vdesselwout/blade-scraper/drawings/v7/bottom.png

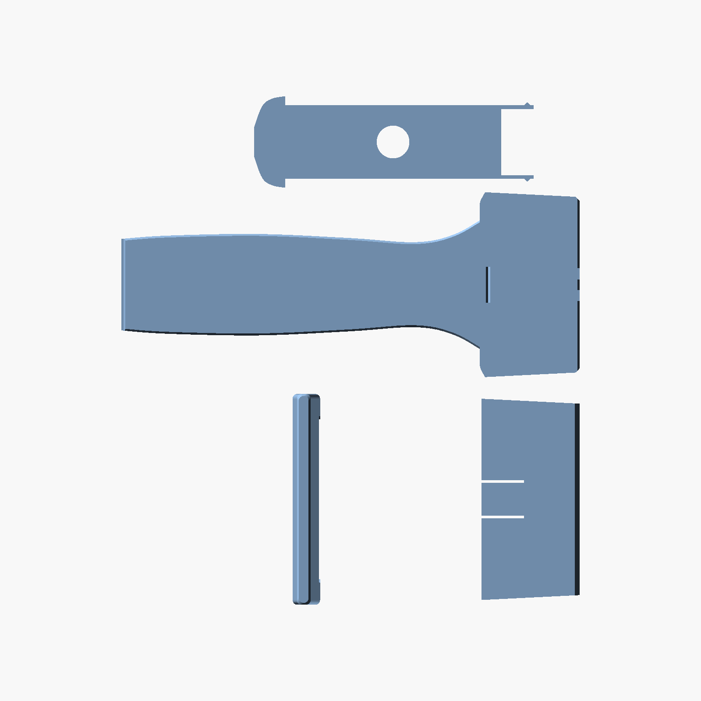
drawings/v7/bottom.png
