vdesselwout/blade-scraper/drawings/v7/drawing.png

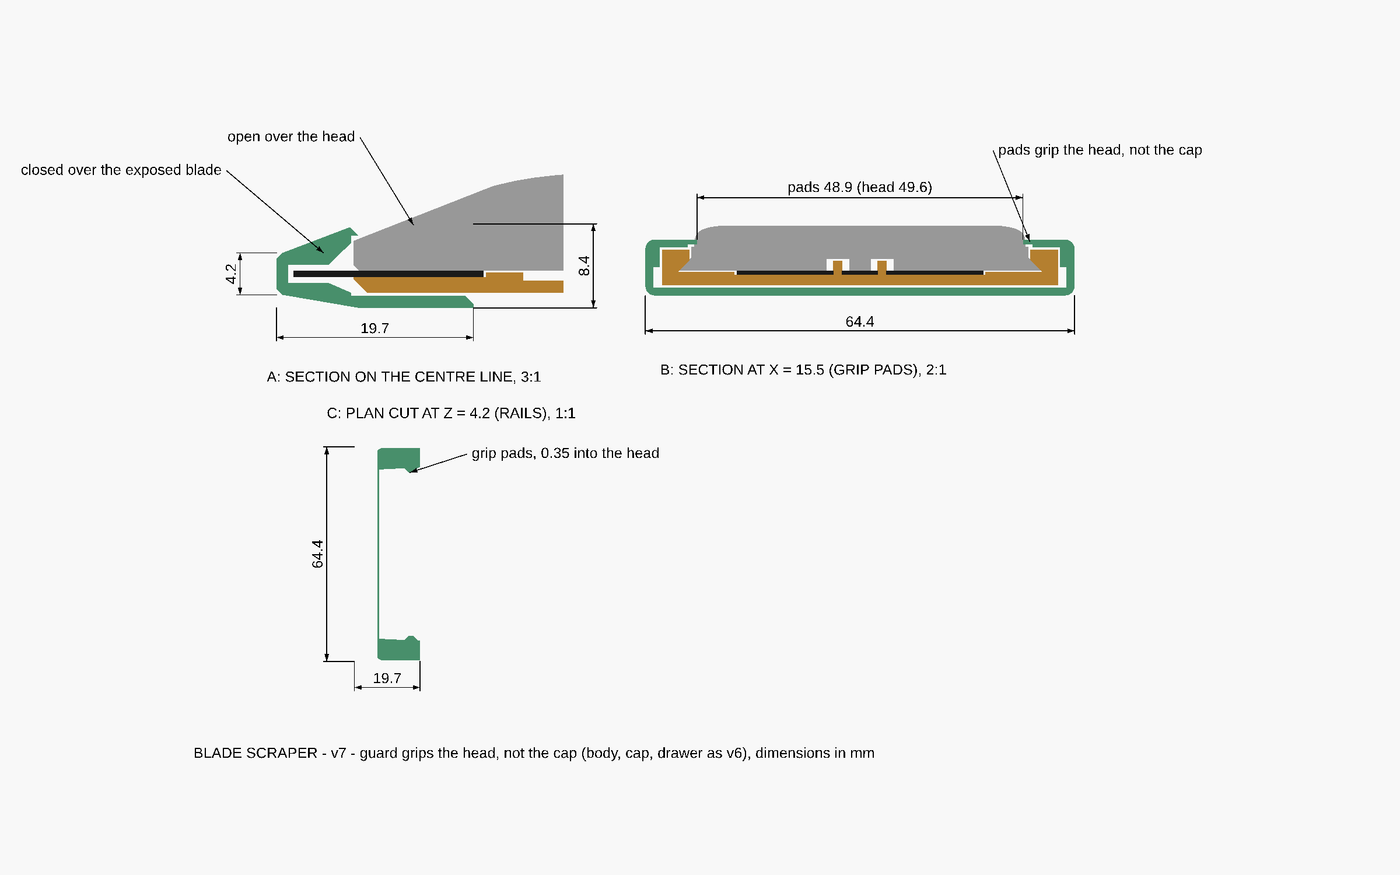
drawings/v7/drawing.png
