vdesselwout/blade-scraper/drawings/v7/guard-bottom.png

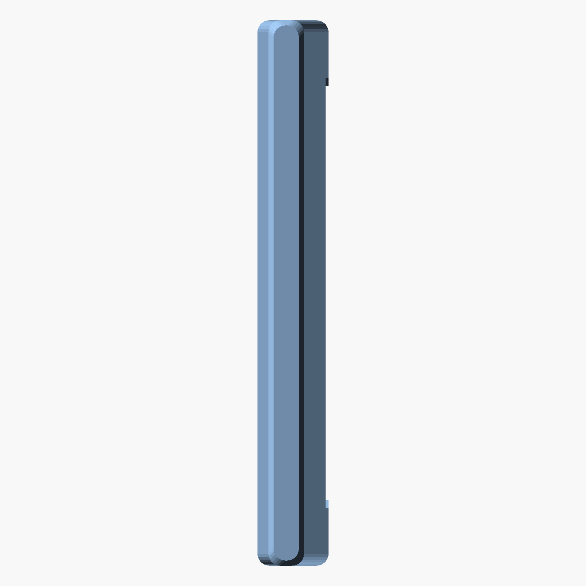
drawings/v7/guard-bottom.png
