vdesselwout/blade-scraper/drawings/v7/guard-iso-bottom.png

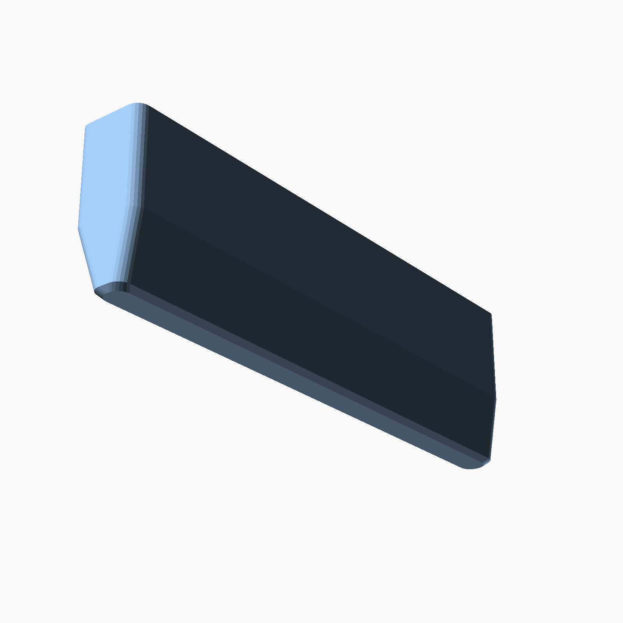
drawings/v7/guard-iso-bottom.png
