vdesselwout/blade-scraper/drawings/v7/guard-iso-top.png

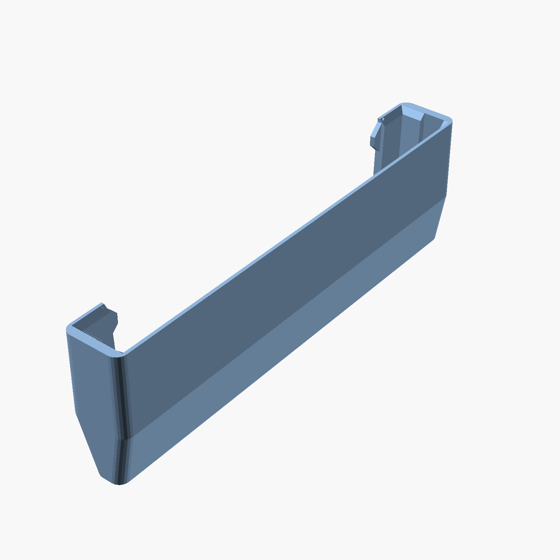
drawings/v7/guard-iso-top.png
