vdesselwout/blade-scraper/drawings/v7/guard-section-3d.png

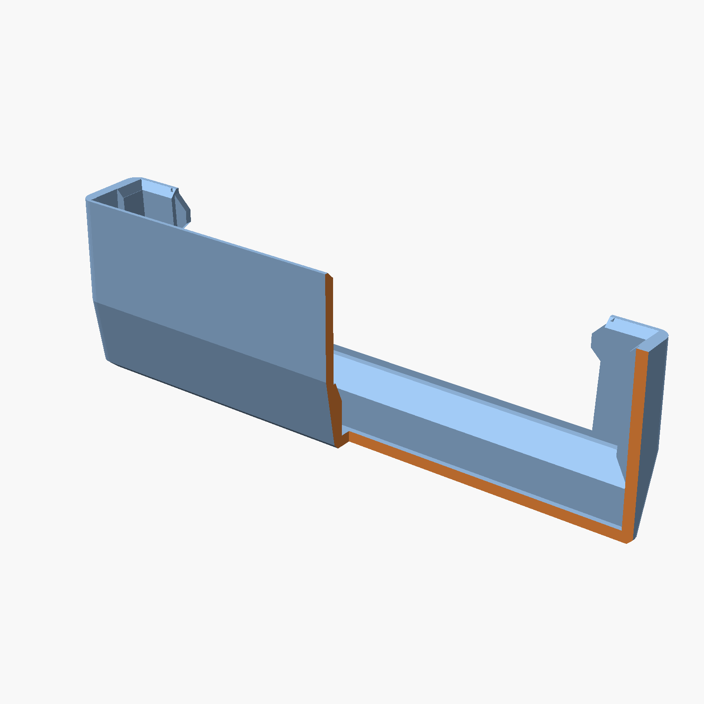
drawings/v7/guard-section-3d.png
