vdesselwout/blade-scraper/drawings/v7/guard-side.png

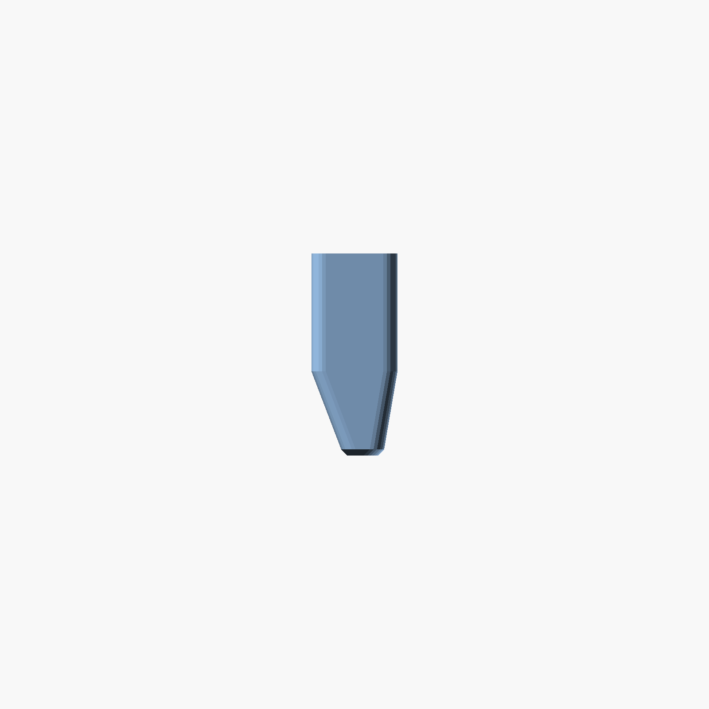
drawings/v7/guard-side.png
