vdesselwout/blade-scraper/drawings/v7/guard-top.png

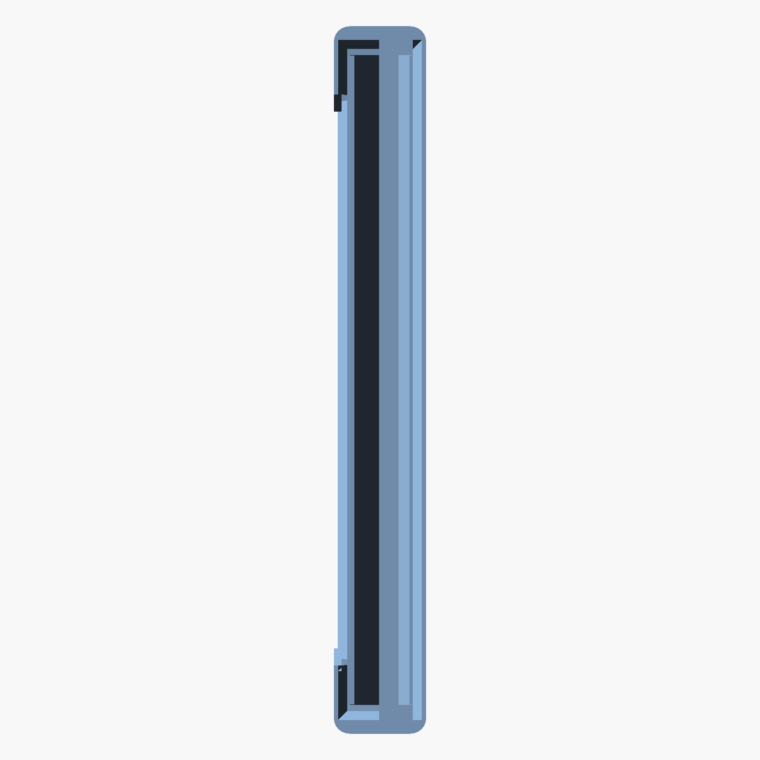
drawings/v7/guard-top.png
