vdesselwout/blade-scraper/drawings/v7/iso-bottom.png

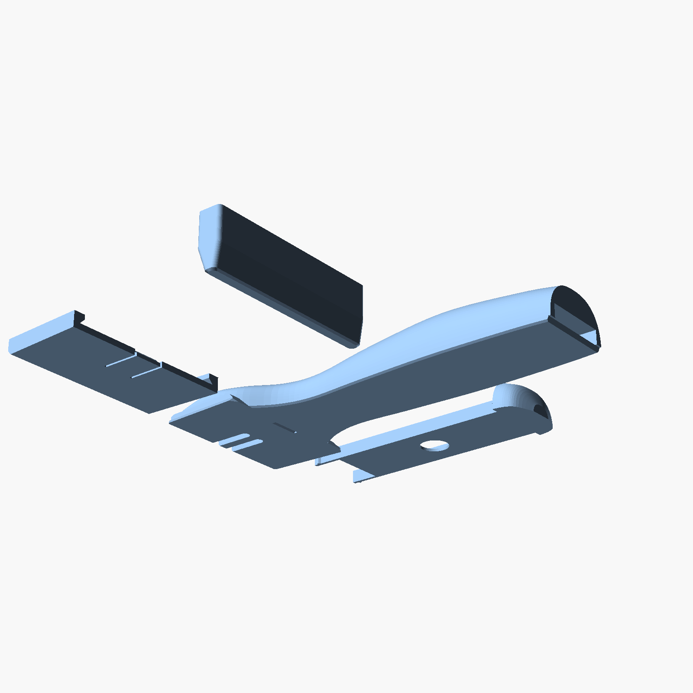
drawings/v7/iso-bottom.png
