vdesselwout/blade-scraper/drawings/v7/iso-top.png

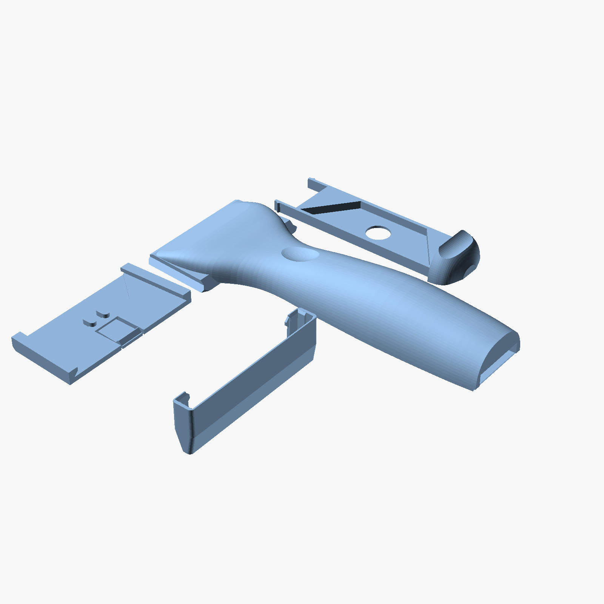
drawings/v7/iso-top.png
