vdesselwout/blade-scraper/drawings/v7/section-3d.png

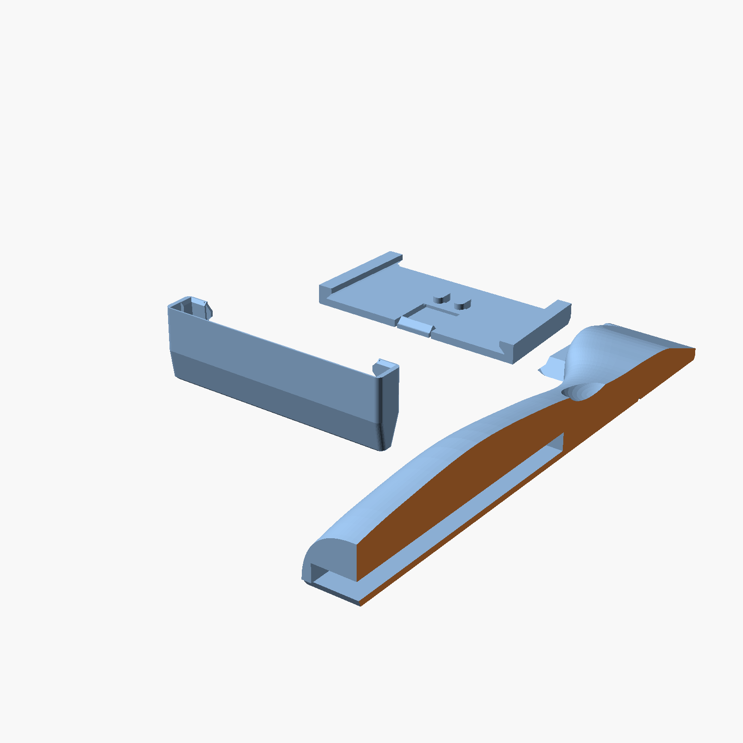
drawings/v7/section-3d.png
