vdesselwout/blade-scraper/drawings/v7/side.png

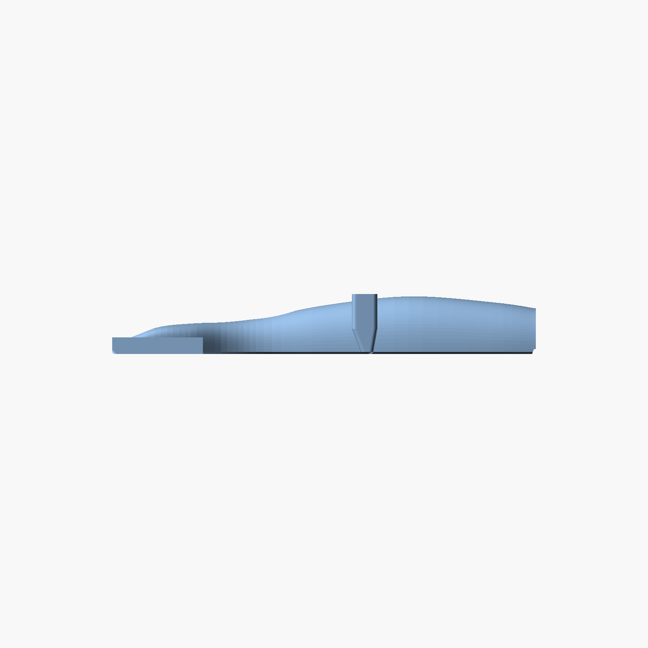
drawings/v7/side.png
