vdesselwout/blade-scraper/drawings/v7/top.png

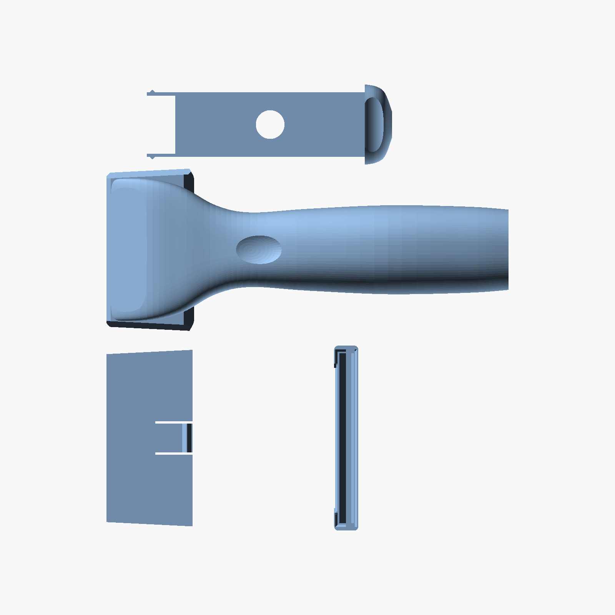
drawings/v7/top.png
