vdesselwout/blade-scraper/drawings/v7/guard-test-bottom.png

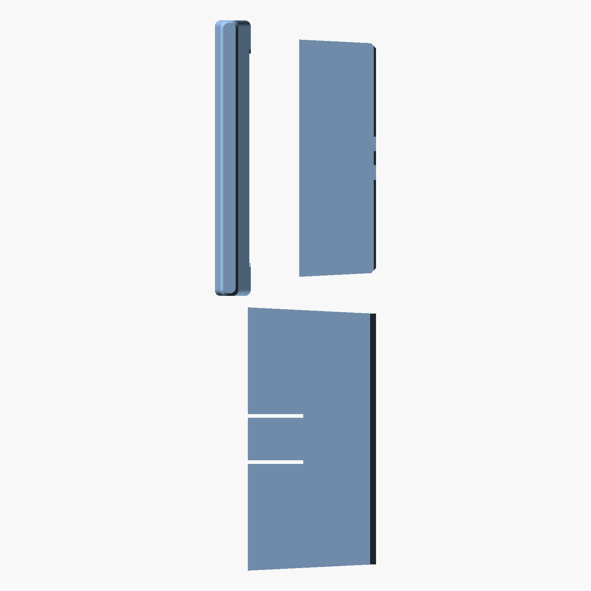
drawings/v7/guard-test-bottom.png
