vdesselwout/blade-scraper/drawings/v7/guard-test-iso-bottom.png

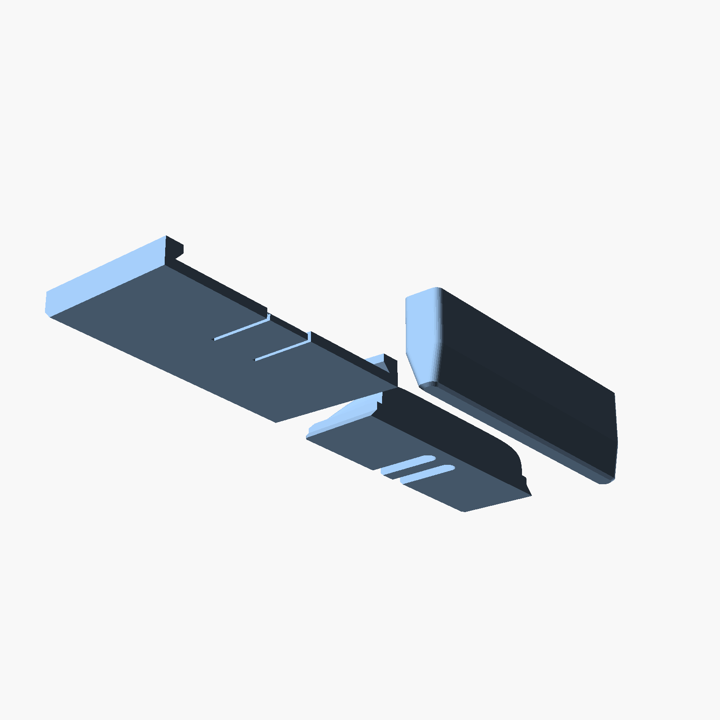
drawings/v7/guard-test-iso-bottom.png
