vdesselwout/blade-scraper/drawings/v7/guard-test-iso-top.png

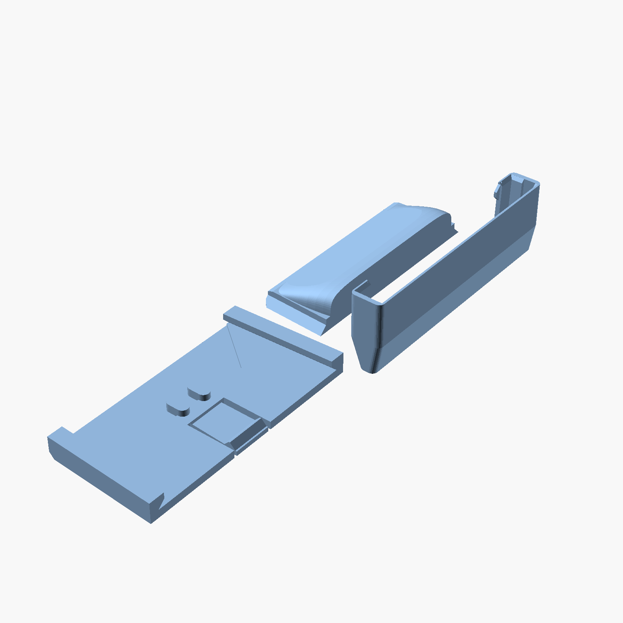
drawings/v7/guard-test-iso-top.png
