vdesselwout/blade-scraper/drawings/v7/guard-test-section-3d.png

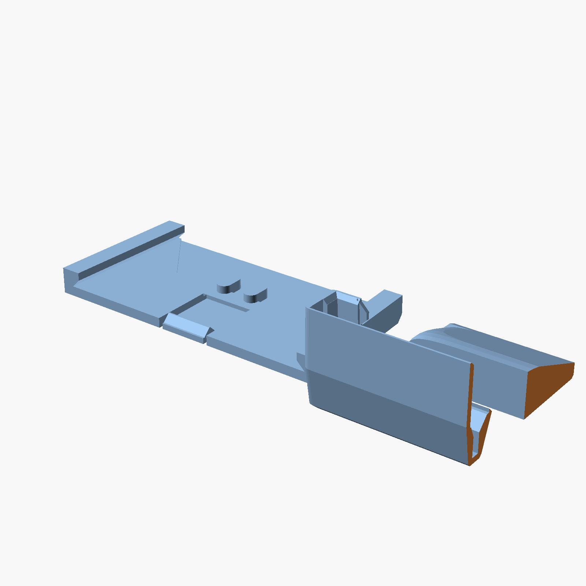
drawings/v7/guard-test-section-3d.png
