vdesselwout/blade-scraper/drawings/v7/guard-test-side.png

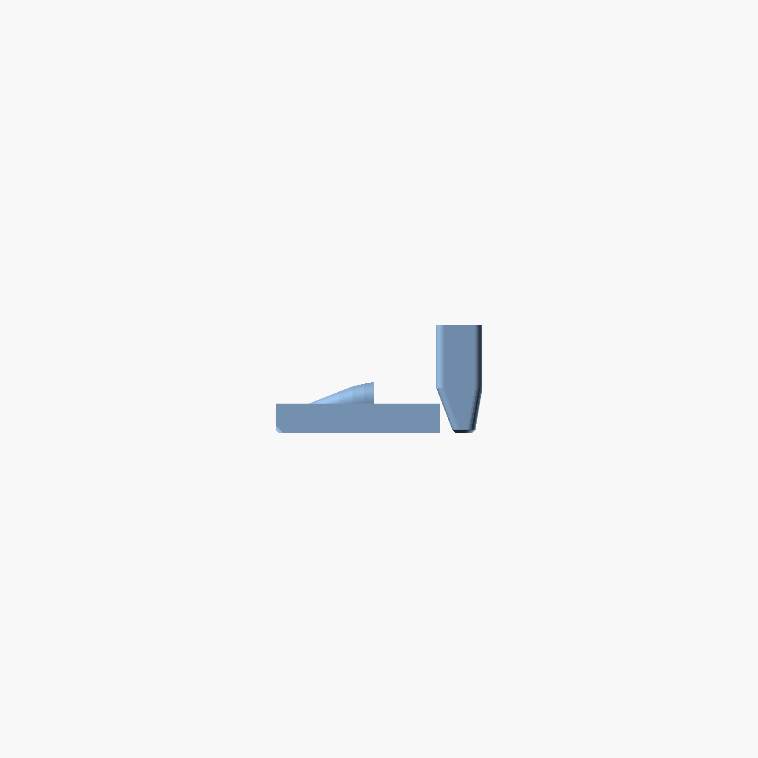
drawings/v7/guard-test-side.png
